capitandirt/micro_M_bI_LLI/ArduinoCode/include/Drivers/Motor.h

#ifndef _MOTOR_H_
#define _MOTOR_H_

#include "Arduino.h"
#include "Config.h"
#include "Battery.h"

struct MotorConnectionParams{
    uint8_t
        DIR, 
        PWM,
        M_POLARITY;
    Battery* _battery;
};

class Motor : public MotorConnectionParams{
public:
    Motor(MotorConnectionParams* mcp) : MotorConnectionParams(*mcp){}
    void init();
    void drive(float u);
};

#endif // !_MOTOR_H_
