capitandirt/micro_M_bI_LLI/ArduinoCode/src/Drivers/Motor.cpp

#include "Drivers/Motor.h"

void Motor::init(){
    pinMode(DIR, OUTPUT);
    pinMode(PWM, OUTPUT);
}

void Motor::drive(float u){
    int16_t pwm = constrain(255.0 * u / _battery->getVoltage(), -255, 255);
    if (pwm >= 0){
        digitalWrite(DIR, M_POLARITY);
        analogWrite(PWM, pwm);
    }
    else{
        digitalWrite(DIR, !M_POLARITY);
        analogWrite(PWM, -pwm);
    }
}
