capitandirt/micro_M_bI_LLI/ArduinoCode/src/Solver.cpp

#include "Solver.h"

void Solver::calc_path(const uint8_t ind_s, const uint8_t ind_f){
    uint8_t cur_cell_ind = ind_s;
    uint8_t cur_x, cur_y;

    WAS_UNDEF_CELL = 0;

    _maze->ClearPath();
    while(cur_cell_ind != ind_f){
        cur_x = cur_cell_ind % MAZE_SIDE_LENGTH;
        cur_y = cur_cell_ind / MAZE_SIDE_LENGTH;

        if(!WAS_UNDEF_CELL && _maze->UndefWallInCell({cur_x, cur_y})){
            WAS_UNDEF_CELL = 1;
            _first_undef_cell_coords = {cur_x, cur_y};
        }

        _maze->GetCellDir(_buf_cell_dir, {cur_x, cur_y});  
        _maze->PushBackPathDir(_buf_cell_dir.cell_dir);

        switch (_buf_cell_dir.cell_dir)
        {
        case Direction::N:
            cur_cell_ind -= MAZE_SIDE_LENGTH;
            break;

        case Direction::E:
            cur_cell_ind++;
            break;

        case Direction::S:
            cur_cell_ind += MAZE_SIDE_LENGTH;
            break;

        case Direction::W:
            cur_cell_ind--;
            break;
        }
    }

    if(!WAS_UNDEF_CELL){
        _first_undef_cell_coords = Maze::IndToVec2(ind_f);
    }
}

void Solver::MazeTestConfig(){
    _maze->SetCell({WallState::LO, WallState::HI, WallState::LO, WallState::HI}, {0, 0});
    _maze->SetCell({WallState::LO, WallState::LO, WallState::LO, WallState::LO}, {2, 0});
    _maze->SetCell({WallState::HI, WallState::LO, WallState::HI, WallState::LO}, {4, 0});
    _maze->SetCell({WallState::LO, WallState::LO, WallState::LO, WallState::HI}, {6, 0});
    _maze->SetCell({WallState::HI, WallState::LO, WallState::HI, WallState::LO}, {8, 0});
    _maze->SetCell({WallState::LO, WallState::HI, WallState::HI, WallState::LO}, {1, 1});
    _maze->SetCell({WallState::LO, WallState::LO, WallState::HI, WallState::HI}, {3, 1});
    _maze->SetCell({WallState::LO, WallState::HI, WallState::LO, WallState::HI}, {5, 1});
    _maze->SetCell({WallState::LO, WallState::HI, WallState::LO, WallState::HI}, {7, 1});
    _maze->SetCell({WallState::HI, WallState::HI, WallState::LO, WallState::HI}, {9, 1});
    _maze->SetCell({WallState::HI, WallState::HI, WallState::LO, WallState::HI}, {0, 2});
    _maze->SetCell({WallState::LO, WallState::HI, WallState::LO, WallState::LO}, {2, 2});
    _maze->SetCell({WallState::HI, WallState::LO, WallState::HI, WallState::LO}, {4, 2});
    _maze->SetCell({WallState::HI, WallState::LO, WallState::LO, WallState::HI}, {6, 2});
    _maze->SetCell({WallState::LO, WallState::HI, WallState::HI, WallState::LO}, {8, 2});
    _maze->SetCell({WallState::HI, WallState::LO, WallState::HI, WallState::LO}, {1, 3});
    _maze->SetCell({WallState::LO, WallState::LO, WallState::HI, WallState::LO}, {3, 3});
    _maze->SetCell({WallState::HI, WallState::LO, WallState::HI, WallState::LO}, {5, 3});
    _maze->SetCell({WallState::HI, WallState::LO, WallState::HI, WallState::LO}, {7, 3});
    _maze->SetCell({WallState::LO, WallState::HI, WallState::LO, WallState::LO}, {9, 3});
    _maze->SetCell({WallState::HI, WallState::LO, WallState::LO, WallState::HI}, {0, 4});
    _maze->SetCell({WallState::LO, WallState::HI, WallState::HI, WallState::LO}, {2, 4});
    _maze->SetCell({WallState::LO, WallState::LO, WallState::LO, WallState::HI}, {4, 4});
    _maze->SetCell({WallState::HI, WallState::LO, WallState::HI, WallState::LO}, {6, 4});
    _maze->SetCell({WallState::LO, WallState::HI, WallState::HI, WallState::LO}, {8, 4});
    _maze->SetCell({WallState::HI, WallState::LO, WallState::HI, WallState::LO}, {1, 5});
    _maze->SetCell({WallState::LO, WallState::HI, WallState::LO, WallState::HI}, {3, 5});
    _maze->SetCell({WallState::LO, WallState::HI, WallState::LO, WallState::HI}, {5, 5});
    _maze->SetCell({WallState::LO, WallState::HI, WallState::HI, WallState::LO}, {7, 5});
    _maze->SetCell({WallState::LO, WallState::HI, WallState::LO, WallState::HI}, {9, 5});
    _maze->SetCell({WallState::LO, WallState::HI, WallState::LO, WallState::HI}, {0, 6});
    _maze->SetCell({WallState::LO, WallState::LO, WallState::HI, WallState::HI}, {2, 6});
    _maze->SetCell({WallState::LO, WallState::HI, WallState::LO, WallState::LO}, {4, 6});
    _maze->SetCell({WallState::HI, WallState::LO, WallState::HI, WallState::LO}, {6, 6});
    _maze->SetCell({WallState::LO, WallState::LO, WallState::LO, WallState::HI}, {8, 6});
    _maze->SetCell({WallState::LO, WallState::HI, WallState::LO, WallState::HI}, {1, 7});
    _maze->SetCell({WallState::HI, WallState::LO, WallState::HI, WallState::LO}, {3, 7});
    _maze->SetCell({WallState::HI, WallState::LO, WallState::HI, WallState::LO}, {5, 7});
    _maze->SetCell({WallState::LO, WallState::HI, WallState::LO, WallState::LO}, {7, 7});
    _maze->SetCell({WallState::HI, WallState::HI, WallState::HI, WallState::LO}, {9, 7});
    _maze->SetCell({WallState::LO, WallState::HI, WallState::LO, WallState::HI}, {0, 8});
    _maze->SetCell({WallState::LO, WallState::LO, WallState::LO, WallState::HI}, {2, 8});
    _maze->SetCell({WallState::HI, WallState::LO, WallState::LO, WallState::LO}, {4, 8});
    _maze->SetCell({WallState::HI, WallState::LO, WallState::HI, WallState::LO}, {6, 8});
    _maze->SetCell({WallState::HI, WallState::LO, WallState::LO, WallState::HI}, {8, 8});
    _maze->SetCell({WallState::LO, WallState::HI, WallState::LO, WallState::LO}, {1, 9});
    _maze->SetCell({WallState::HI, WallState::LO, WallState::HI, WallState::HI}, {3, 9});
    _maze->SetCell({WallState::HI, WallState::LO, WallState::LO, WallState::LO}, {5, 9});
    _maze->SetCell({WallState::HI, WallState::LO, WallState::LO, WallState::LO}, {7, 9});
    _maze->SetCell({WallState::HI, WallState::HI, WallState::HI, WallState::LO}, {9, 9});
    _maze->SetCell({WallState::HI, WallState::HI, WallState::LO, WallState::HI}, {0, 0});
    _maze->SetCell({WallState::LO, WallState::HI, WallState ::HI, WallState::LO},{5, 10});
    _maze->SetCell({WallState::HI, WallState::HI, WallState::LO, WallState::LO}, {5, 9});
    _maze->SetCell({WallState::HI, WallState::LO, WallState::HI, WallState::LO}, {4, 9});
    _maze->SetCell({WallState::LO, WallState::HI, WallState::HI, WallState::LO}, {1, 9});
    _maze->SetCell({WallState::LO, WallState::LO, WallState::HI, WallState::LO}, {8, 9});
    _maze->SetCell({WallState::LO, WallState::LO, WallState::HI, WallState::LO}, {7, 9});

    _maze->PrimaryFill();
}

void Solver::ExplorerSolveBfsMaze(const Vec2 start, const Vec2 finish){
    uint8_t ind_s = Maze::Vec2ToInd(start);    
    uint8_t ind_f = Maze::Vec2ToInd(finish);
    
    _maze->UndefDirs();
    _queue.clear();

    _queue.pushBack(ind_f);

    while(!_queue.isEmpty()){
        uint8_t cur_cell_ind = _queue.popFront();

        if(cur_cell_ind == ind_s){
            break;
        }

        Cell cur_cell;
        Vec2 cur_cell_vec2 = Maze::IndToVec2(cur_cell_ind);
        _maze->GetCell(cur_cell, cur_cell_vec2);

        if(cur_cell.north_wall != WallState::HI){
            Vec2 checked_cell_vec = {cur_cell_vec2.x, cur_cell_vec2.y - 1};

            _maze->GetCellDir(_buf_cell_dir, checked_cell_vec);
            
            if(_buf_cell_dir.is_def_cell_dir != DirectionState::DEF){
                _maze->SetCellDir(Direction::S, checked_cell_vec);

                _queue.pushBack(cur_cell_ind - MAZE_SIDE_LENGTH); // cur_y--
            }
        }

        if(cur_cell.east_wall != WallState::HI){
            Vec2 checked_cell_vec = {cur_cell_vec2.x + 1, cur_cell_vec2.y};

            _maze->GetCellDir(_buf_cell_dir, checked_cell_vec);

            if(_buf_cell_dir.is_def_cell_dir != DirectionState::DEF){
                _maze->SetCellDir(Direction::W, checked_cell_vec);
                _queue.pushBack(cur_cell_ind + 1); // cur_x++
            }
        }

        if(cur_cell.south_wall != WallState::HI){
            Vec2 checked_cell_vec = {cur_cell_vec2.x, cur_cell_vec2.y + 1};

            _maze->GetCellDir(_buf_cell_dir, checked_cell_vec);

            if(_buf_cell_dir.is_def_cell_dir != DirectionState::DEF){
                _maze->SetCellDir(Direction::N, checked_cell_vec);
                _queue.pushBack(cur_cell_ind + MAZE_SIDE_LENGTH); // cur_y++
            }
        }

        if(cur_cell.west_wall != WallState::HI){
            Vec2 checked_cell_vec = {cur_cell_vec2.x - 1, cur_cell_vec2.y};

            _maze->GetCellDir(_buf_cell_dir, checked_cell_vec);

            if(_buf_cell_dir.is_def_cell_dir != DirectionState::DEF){
                _maze->SetCellDir(Direction::E, checked_cell_vec);
                _queue.pushBack(cur_cell_ind - 1); // cur_x--
            }
        }
    }

    _maze->UndefCell(finish);

    calc_path(ind_s, ind_f);
}

void Solver::FastSolveBfsMaze(const Vec2 start, const Vec2 finish){
    uint8_t ind_s = Maze::Vec2ToInd(start);    
    uint8_t ind_f = Maze::Vec2ToInd(finish);
    
    _maze->UndefDirs();
    _queue.clear();

    _queue.pushBack(ind_f);

    while(!_queue.isEmpty()){
        uint8_t cur_cell_ind = _queue.popFront();

        if(cur_cell_ind == ind_s){
            break;
        }

        Cell cur_cell;
        Vec2 cur_cell_vec2 = Maze::IndToVec2(cur_cell_ind);
        _maze->GetCell(cur_cell, cur_cell_vec2);

        if(cur_cell.north_wall != WallState::HI && cur_cell.north_wall != WallState::UNDEF){
            Vec2 checked_cell_vec = {cur_cell_vec2.x, cur_cell_vec2.y - 1};

            _maze->GetCellDir(_buf_cell_dir, checked_cell_vec);
            
            if(_buf_cell_dir.is_def_cell_dir != DirectionState::DEF){
                _maze->SetCellDir(Direction::S, checked_cell_vec);

                _queue.pushBack(cur_cell_ind - MAZE_SIDE_LENGTH); // cur_y--
            }
        }

        if(cur_cell.east_wall != WallState::HI && cur_cell.east_wall != WallState::UNDEF){
            Vec2 checked_cell_vec = {cur_cell_vec2.x + 1, cur_cell_vec2.y};

            _maze->GetCellDir(_buf_cell_dir, checked_cell_vec);

            if(_buf_cell_dir.is_def_cell_dir != DirectionState::DEF){
                _maze->SetCellDir(Direction::W, checked_cell_vec);
                _queue.pushBack(cur_cell_ind + 1); // cur_x++
            }
        }

        if(cur_cell.south_wall != WallState::HI && cur_cell.south_wall != WallState::UNDEF){
            Vec2 checked_cell_vec = {cur_cell_vec2.x, cur_cell_vec2.y + 1};

            _maze->GetCellDir(_buf_cell_dir, checked_cell_vec);

            if(_buf_cell_dir.is_def_cell_dir != DirectionState::DEF){
                _maze->SetCellDir(Direction::N, checked_cell_vec);
                _queue.pushBack(cur_cell_ind + MAZE_SIDE_LENGTH); // cur_y++
            }
        }

        if(cur_cell.west_wall != WallState::HI && cur_cell.west_wall != WallState::UNDEF){
            Vec2 checked_cell_vec = {cur_cell_vec2.x - 1, cur_cell_vec2.y};

            _maze->GetCellDir(_buf_cell_dir, checked_cell_vec);

            if(_buf_cell_dir.is_def_cell_dir != DirectionState::DEF){
                _maze->SetCellDir(Direction::E, checked_cell_vec);
                _queue.pushBack(cur_cell_ind - 1); // cur_x--
            }
        }
    }

    _maze->UndefCell(finish);

    calc_path(ind_s, ind_f);
}

Vec2 Solver::firstUndefCellCoords(){
    return _first_undef_cell_coords;
}
