capitandirt/micro_M_bI_LLI/ArduinoCode/include/PiReg.h

#ifndef _PI_REGULATOR_H_
#define _PI_REGULATOR_H_

#include "Config.h"
#include "Drivers/VelocityEstimator.h"
#include "Arduino.h"
#include "Drivers/Battery.h"

struct PiRegConnectionParams{
    float Kp;
    float Ki;
    Battery* battery;
};

class PiReg : public PiRegConnectionParams{
public:
    PiReg(PiRegConnectionParams *prcp) : PiRegConnectionParams(*prcp){}     

    void passSet(float& set);
    void passCur(float& cur);  
    float getU() const;

    void reload();
    void tick(); 

private:
    static constexpr float VOLTAGE_ERROR = 0.2;

    float _integrator = 0;
    
    float _set = 0;
    float _cur = 0;

    float _err = 0;
    float _P = 0;
    float _I = 0;

    float _u = 0;
    float _constrained_u = 0;
};

#endif // !_PI_REGULATOR_H_
