capitandirt/micro_M_bI_LLI/ArduinoCode/src/Odometry.cpp

#include "Odometry.h"

float Odometry::getX() const{
    return X.getOut();
}

float Odometry::getY() const{
    return Y.getOut();
}

float Odometry::getTheta() const{
    return Theta.getOut();
}

float Odometry::setTheta(float theta_) noexcept{
    Theta = theta_;
}

float Odometry::getDist() const{
    return Distance.getOut();
}

float Odometry::getRelativeX() const{
    return X_r.getOut();
}

float Odometry::getRelativeY() const{
    return Y_r.getOut();
}

float Odometry::getRelativeTheta() const{
    return Theta_r.getOut();
}

float Odometry::getRelativeDist() const{
    return Distance_r.getOut();
}

Vec2 Odometry::getMazeCoords() const{
    return mazeCoords;
}

Direction Odometry::getDir() const{
    return dir;
}

Direction Odometry::getStartFastDir() const{
    return startFastDir;
}

void Odometry::setDir(Direction dir_) noexcept{
    dir = dir_;
}

void Odometry:: setRelativeDist(float val){
    Distance_r = val;
}

void Odometry::printMazeCoords() const{
    Serial.print(mazeCoords.x);
    Serial.print(" ");
    Serial.println(mazeCoords.y);
}

void Odometry::printDir() const{
    switch (dir)
    {
    case Direction::N:
        Serial.println("N");
        break;
    case Direction::S:
        Serial.println("S");
        break;
    case Direction::E:
        Serial.println("E");
        break;
    case Direction::W:
        Serial.println("W");
        break;
    }
}

void Odometry::tick(float omegaL, float omegaR)
{
    vL = omegaL * WHEEL_RADIUS;
    vR = omegaR * WHEEL_RADIUS;

    float theta_i = (vR - vL) / ROBOT_WIDTH; //в этом вычислении опускается тангенс угла, тк tg(x) ~= x на малых углах
    Theta.tick(theta_i);

    v = (vR + vL) / 2;
    vX = v * cos(Theta.getOut());
    vY = v * sin(Theta.getOut());

    Distance.tick(v);
    X.tick(vX);    
    Y.tick(vY);

    Theta_r.tick(theta_i);
    Distance_r.tick(v);
    X_r.tick(vX);
    X_r.tick(vY);
}

void Odometry::updateMazeCoords(Direction dir){
    mazeCoords.plusOrtVector(dir);
}

void Odometry::updateMazeCoords(Vec2 new_v){
    mazeCoords = new_v;
}

void Odometry::reset()
{
    vL = 0;
    vR = 0;
    vX = 0;
    vY = 0;
    v = 0;
    mazeCoords = {0, 0};
    dir = Direction::N;
    X.reset();
    Y.reset();
    Theta.reset();
    Distance.reset();
}

void Odometry::updateRelative()
{
    X_r = 0;
    Y_r = 0;
    Theta_r = 0;
    Distance_r = 0;
}
