capitandirt/micro_M_bI_LLI/ArduinoCode/include/CycloUtilits/Cyclograms/smart90.h

#ifndef _SMART90_H_
#define _SMART90_H_

#include "CycloUtilits/CycloTypes.h"
#include "Cyclogram.config.h"


CYCLOGRAM(SS90AL)
{
    ms->v_f0 = FAST_FORWARD_SPEED;
    float a = 0;
    static Integrator v = 0;

    float forwDist,
          transitionDist,
          circleDist;
          
    if(s->odometry->getRelativeDist() < forwDist)
    else if(s->odometry->getRelativeDist() > forwDist && s->odometry->getRelativeDist() < forwDist + transitionDist)
    else if(s->odometry->getRelativeDist() > forwDist + transitionDist && s->odometry->getRelativeDist() < forwDist + transitionDist + circleDist)

    v.tick(a.getOut());


}


#endif // !_SMART90_H_
